Brebl/audio-switch/code/src/interrupts.c

#include "main.h"
#include "display.h"
volatile static uint8_t timeout_counter = 0;
const uint8_t timeout_max = 10;           //secs
volatile static uint8_t audioport_counter = 0;
const uint8_t audioport_max = 5;
volatile static enum Mode mode = automatic;

void init_interrupts()
{
    /********************
    8-bit Timer/Counter0:
    clock 128kHz
    *
    prescaler 1024
    --------------
    == clock tick time 8000us
    *
    output compare register 125
    ---------------------------
    == 1Hz
    **********************/
    GIMSK |= (1 << PCIE2);
    PCMSK2 |= (1 << PCINT17);               //push button
    TCCR0A |= (1 << WGM01);                 //ctc
    TCCR0B |= (1 << CS00) | (1 << CS02);    //1024 prescaler
    OCR0A = 0x7d;                           //125
    TIMSK |= (1 << OCIE0A);                 //ocr-a enable
    DDRB |= (1 << PB6);                     //output DO
    PORTB |= (1 << PB5) | (1 << PB7);       //input DI, SCK
    USICR = 0x98;                           //10011000 = USISIE; wiremode:spi; clocksrc:ext-pos.edge
    sei();
    set_sleep_mode(SLEEP_MODE_PWR_DOWN);
    LCD_string(AUDIO1);
    TRAN1(1);
}

//push button logic
/*
Short press: Change port or turn backlight on
Long press: Switch between automatic and manual mode
Very long press: Reset
*/
ISR(PCINT2_vect) {
#define LONG_PRESS 3
#define VERY_LONG_PRESS 10
    uint8_t counter_low = 0;
    uint8_t counter_high = 0;
    uint8_t buttons = debounce(PUSH_BUTTON_PORT);
    set_sleep_mode(SLEEP_MODE_IDLE);
    if (bit_is_clear(buttons, PUSH_BUTTON)) { //button press
        if (bit_is_set(LCD_AK_PORT, LCD_AK_PIN) && mode==manual) { //lcd backlight is on
            timeout_counter = 0;
            audioport_counter++;
            if (audioport_counter >= audioport_max) {
                audioport_counter = 0;
            }
            change_port(audioport_counter);
        }
        else { //turn lcd backlight on
            LCD_AK(1);
            timeout_counter = 0;
        }
        while (bit_is_clear(buttons, PUSH_BUTTON)) { //button is being pressed
            buttons = debounce(PUSH_BUTTON_PORT);
            _delay_ms(5);
            counter_low++;
            if (counter_low > 200) {
                counter_low = 0;
                counter_high++;
                if (counter_high == LONG_PRESS) {
                    change_mode(&mode);
                }
                else if (counter_high == VERY_LONG_PRESS) {
                    LCD_clear_screen();
                    LCD_string("    reset...    ");
                    wdt_enable(WDTO_1S);
                }
            }
        }
    }
}

//power down after timeout_max, LCD off, audioport stays on
ISR(TIMER0_COMPA_vect)
{
    timeout_counter++;
    if (timeout_counter >= timeout_max) {
        timeout_counter = 0;
        LCD_AK(0);
        set_sleep_mode(SLEEP_MODE_PWR_DOWN);
    }
}

//SPI
ISR(USI_START_vect)
{
    if (mode == automatic) {
        LCD_AK(1);
        set_sleep_mode(SLEEP_MODE_IDLE);
        USISR = (1 << USIOIF); //clear overflow flag and counter
        while (!(USISR & (1 << USIOIF))) { ; }
        change_port(USIDR);
        USISR = (1 << USISIF); //clear interrupt flag
    }
}

void change_port(uint8_t new_port)
{
    transistors_off();
    switch (new_port) {
    case 0:
        TRAN1(1);
        LCD_animate(AUDIO1);
        break;
    case 1:
        TRAN2(1);
        LCD_animate(AUDIO2);
        break;
    case 2:
        TRAN3(1);
        LCD_animate(AUDIO3);
        break;
    case 3:
        TRAN4(1);
        LCD_animate(AUDIO4);
        break;
    case 4:
        TRAN5(1);
        LCD_animate(AUDIO5);
        break;
    case 5:
        TRAN6(1);
        LCD_animate(AUDIO6);
        break;
    default:
        break;
    }
}

void change_mode(volatile enum Mode* mode)
{
    switch (*mode) {
    case automatic:
        LCD_animate("  Manual mode   ");
        *mode = manual;
        break;
    case manual:
        LCD_animate(" Automatic mode ");
        *mode = automatic;
        break;
    default:
        break;
    }
}
